iamlite/Ender3V3Mods/Gantry Support Rods/Images/3.png

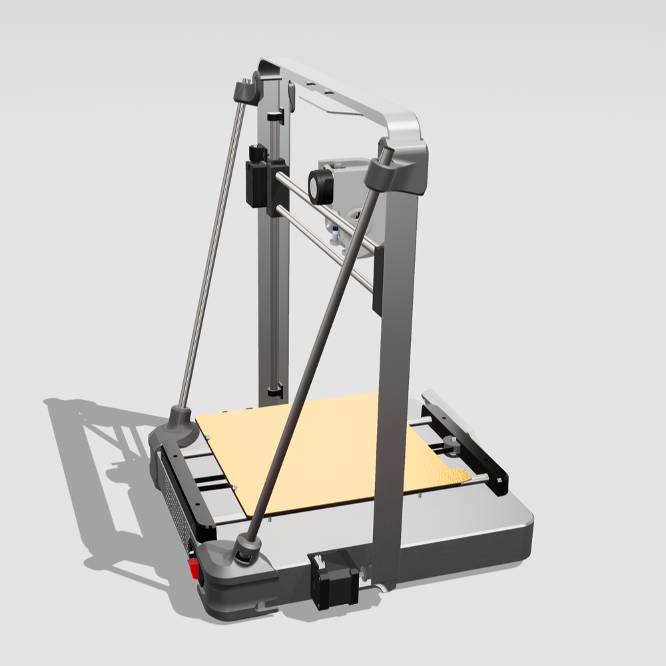
Gantry Support Rods/Images/3.png
