iamlite/Ender3V3Mods/Gantry Support Rods/Images/4.png

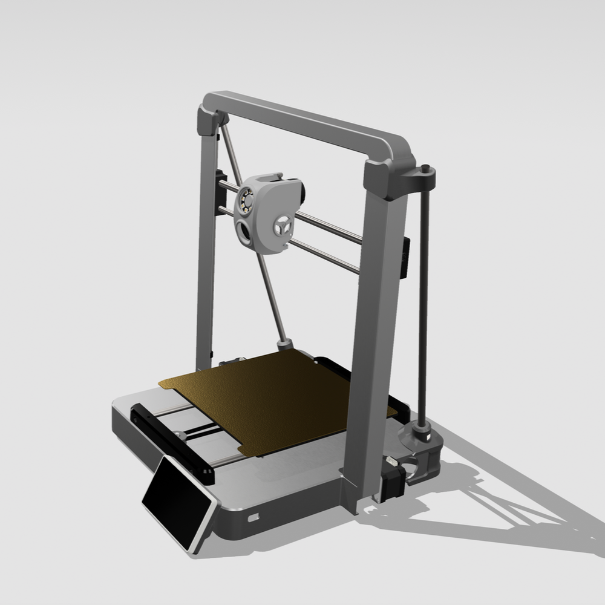
Gantry Support Rods/Images/4.png
