iamlite/Ender3V3Mods/Gantry Support Rods/Images/5.png

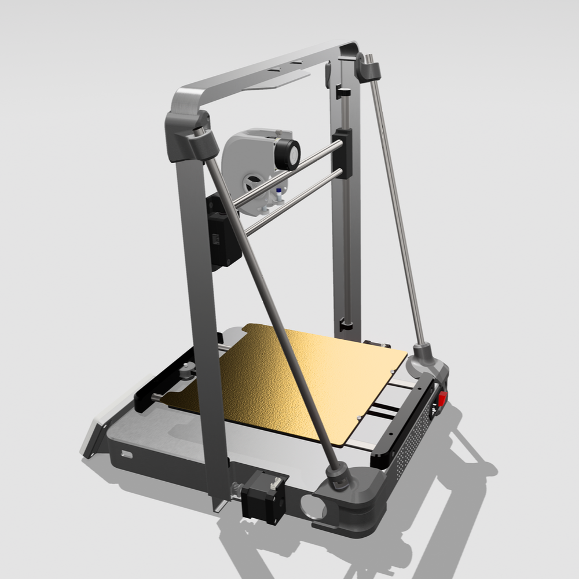
Gantry Support Rods/Images/5.png
