iamlite/Ender3V3Mods/Gantry Support Rods/Images/6.jpeg

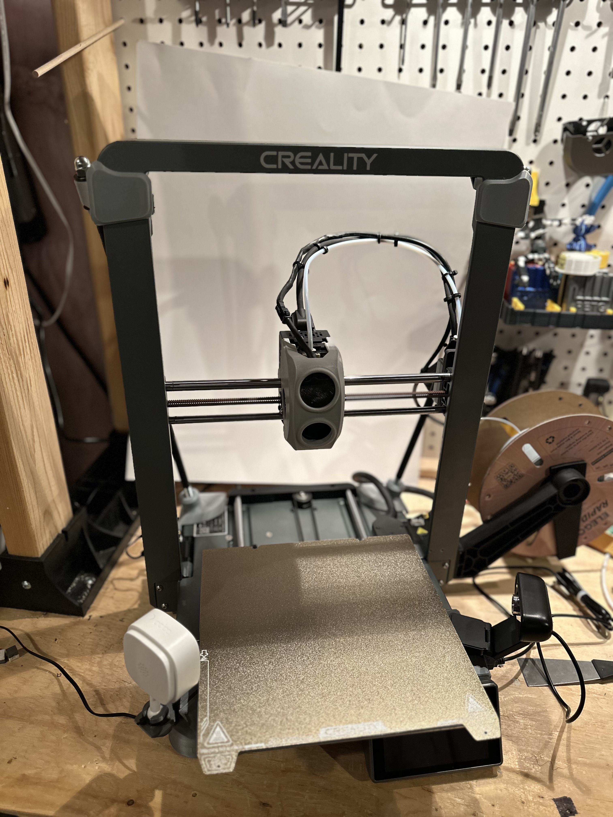
Gantry Support Rods/Images/6.jpeg
