iamlite/Ender3V3Mods/Gantry Support Rods/Images/7.jpeg

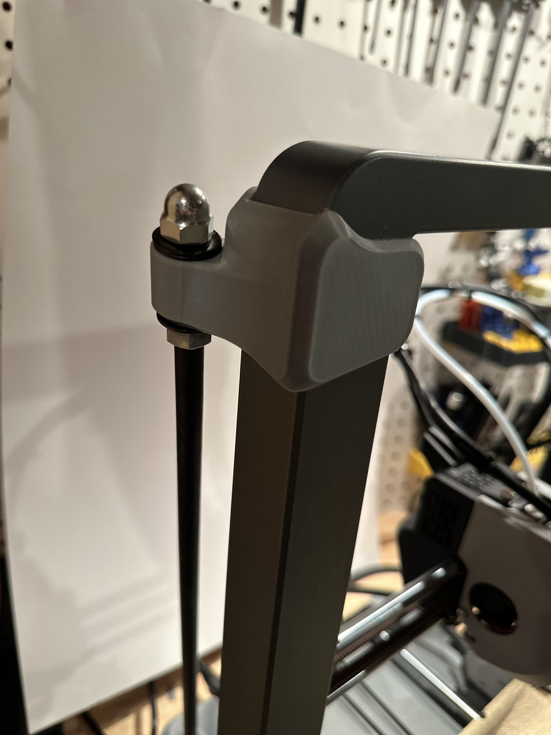
Gantry Support Rods/Images/7.jpeg
