iamlite/Ender3V3Mods/Gantry Support Rods/Images/8.jpeg

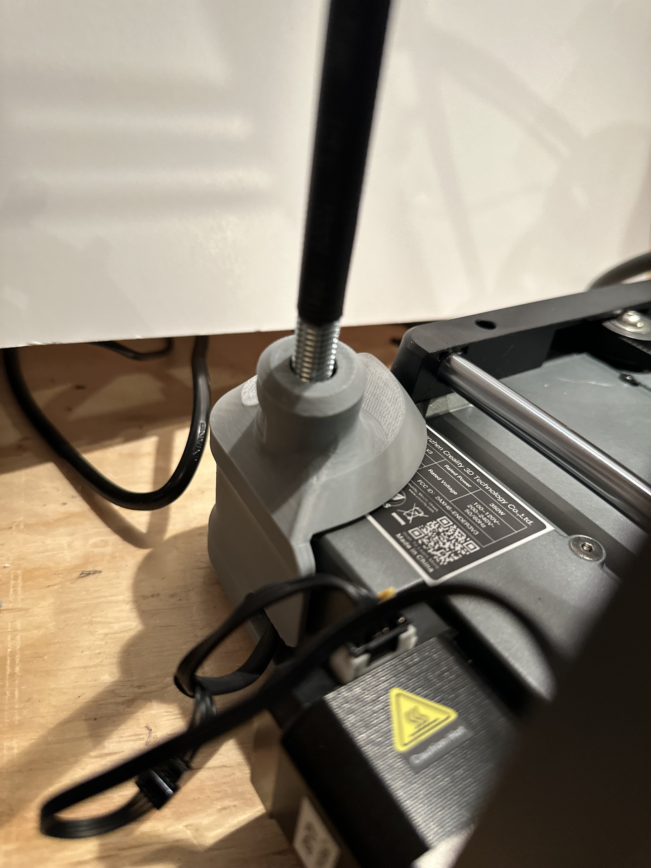
Gantry Support Rods/Images/8.jpeg
