iamlite/Ender3V3Mods/Gantry Support Rods/Images/9.jpeg

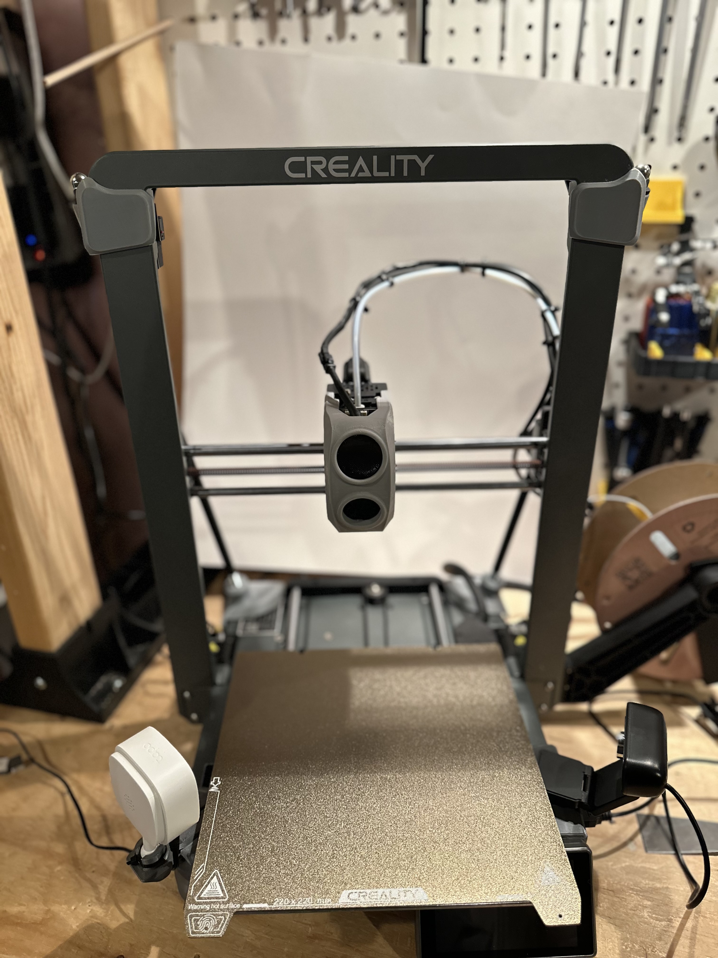
Gantry Support Rods/Images/9.jpeg
